jesseparker/vysko/stl/vysko/bearing_pillow_top_x3.stl

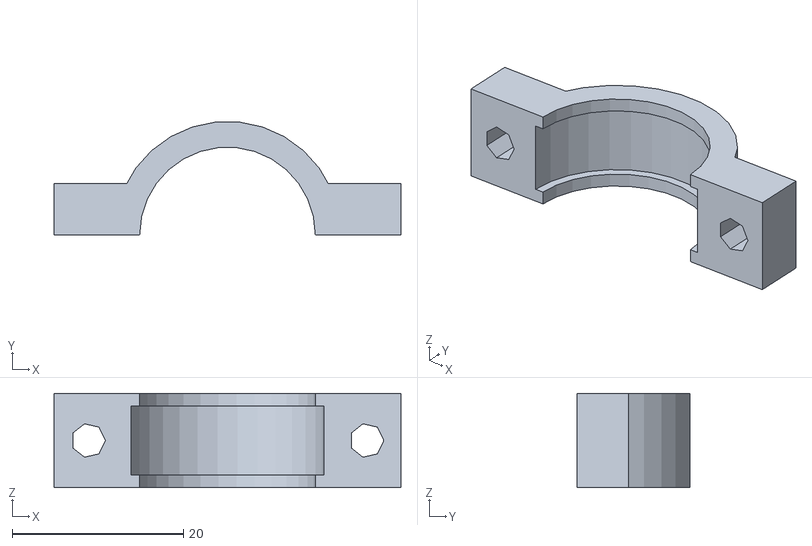
[picture p19: CAD file, 2020-10-01]
stl/vysko/bearing_pillow_top_x3.stl
40.5 x 13.2 x 11.0
