jesseparker/vysko/stl/vysko/funnel.stl

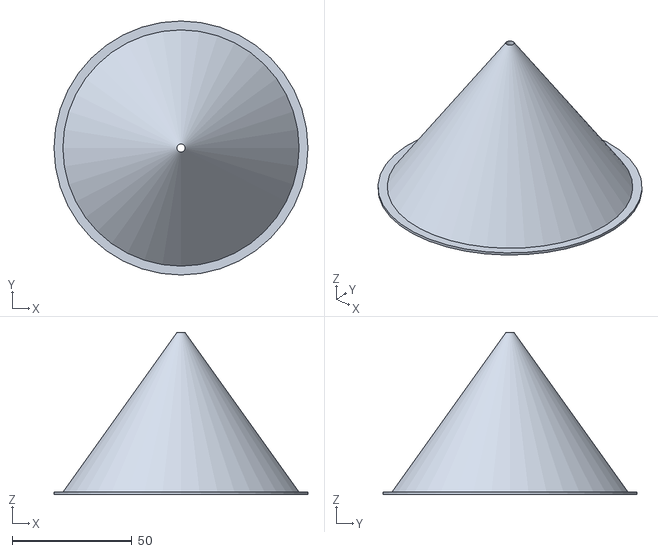
[picture p20: CAD file, 2020-10-01]
stl/vysko/funnel.stl
106.0 x 106.0 x 67.6
