jesseparker/vysko/stl/vysko/spinning_plate_cw.stl

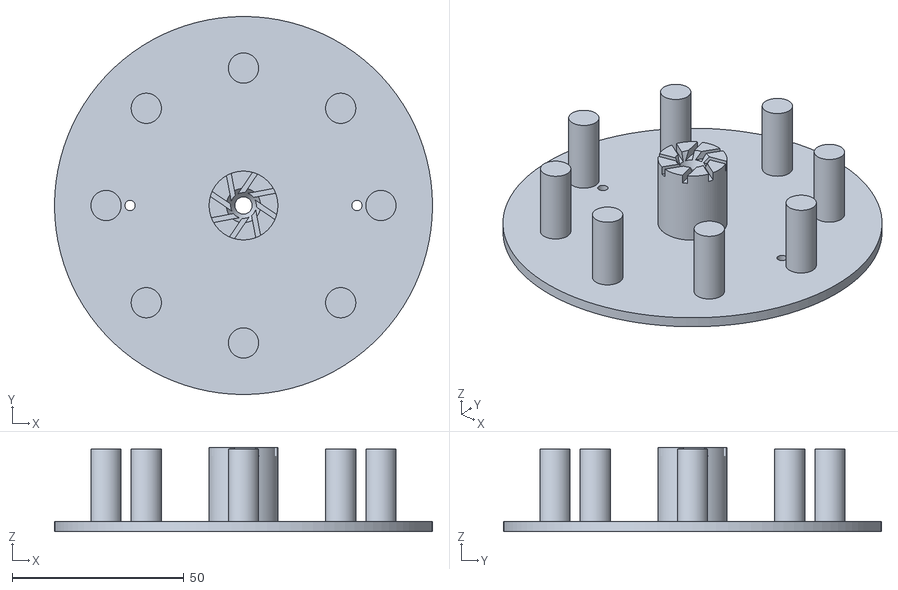
[picture p21: CAD file, 2020-10-01]
stl/vysko/spinning_plate_cw.stl
110.0 x 110.0 x 24.5
