jesseparker/vysko/stl/vysko/strut_drum.stl

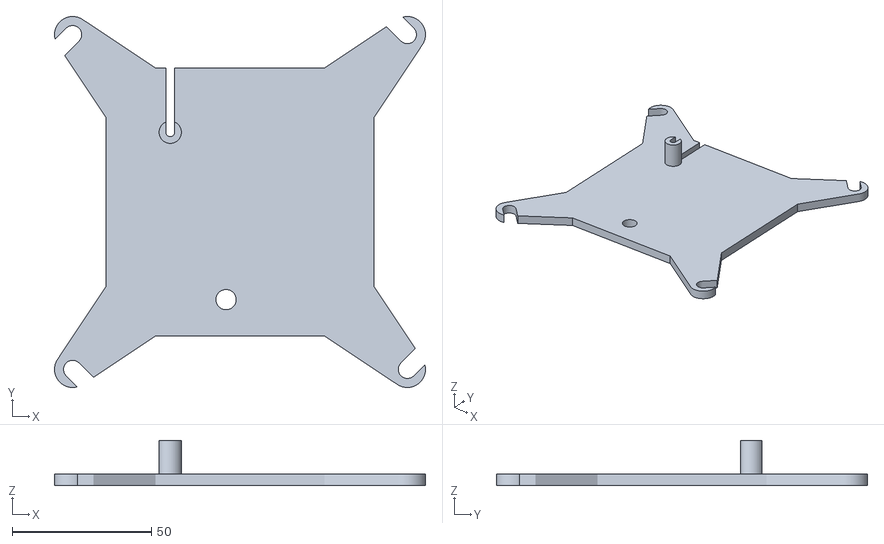
[picture p22: CAD file, 2020-10-01]
stl/vysko/strut_drum.stl
133.0 x 133.0 x 16.2
