jesseparker/vysko/stl/vysko/funnel_strut.stl

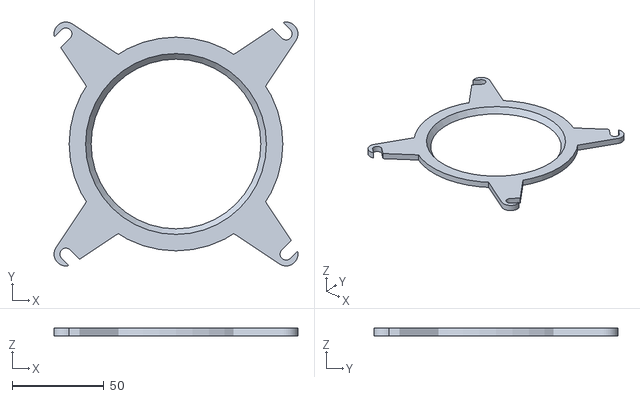
[picture p23: CAD file, 2020-10-01]
stl/vysko/funnel_strut.stl
133.0 x 133.0 x 4.25
