jesseparker/vysko/stl/vysko/strut_c.stl

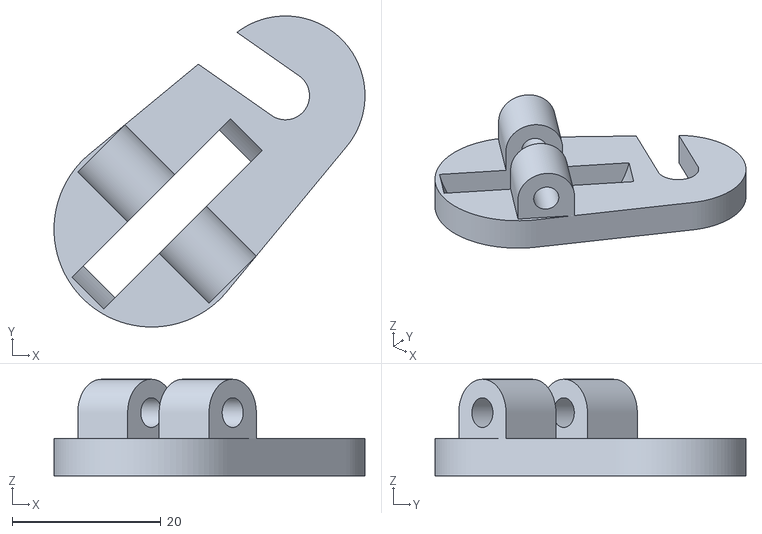
[picture p24: CAD file, 2020-10-01]
stl/vysko/strut_c.stl
41.9 x 41.9 x 13.0
