jesseparker/vysko/stl/vysko/spool_x19.stl

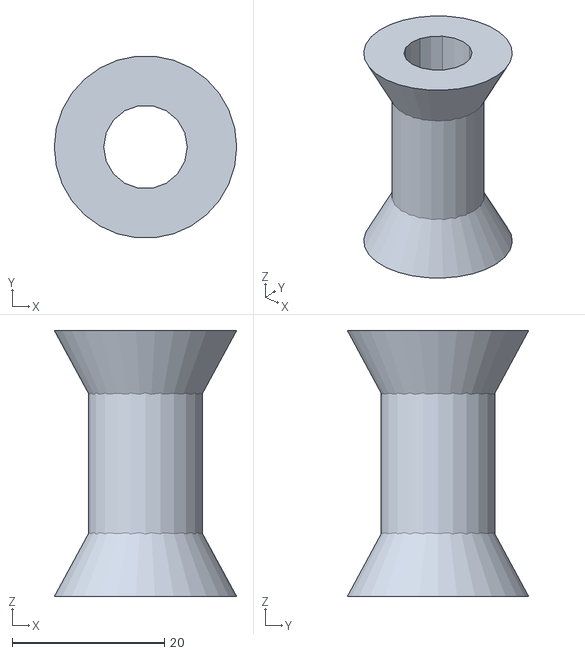
[picture p25: CAD file, 2020-10-01]
stl/vysko/spool_x19.stl
24.0 x 23.9 x 35.0
