jesseparker/vysko/stl/vysko/strut_r45_x3.stl

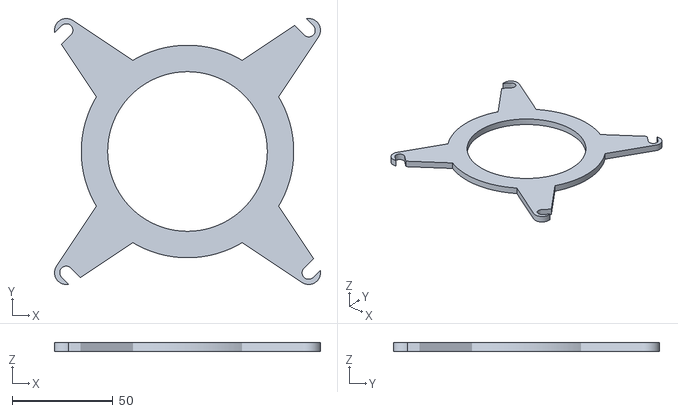
[picture p26: CAD file, 2020-10-01]
stl/vysko/strut_r45_x3.stl
131.7 x 131.7 x 4.25
