jesseparker/vysko/stl/vysko/driveshaft_pulley_20mm_x2.stl

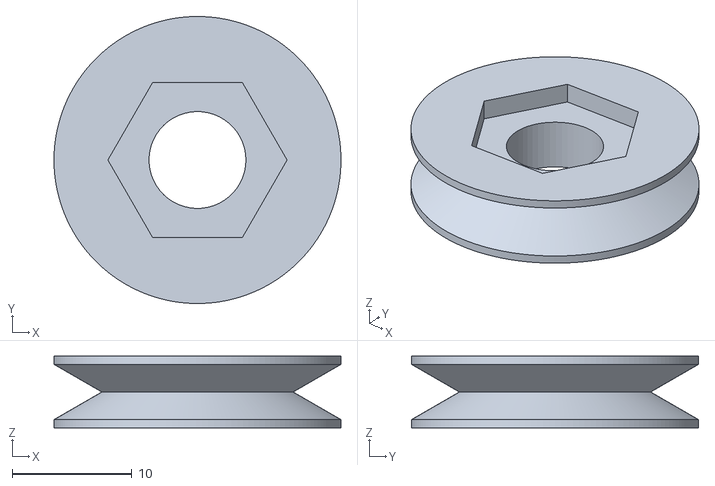
[picture p27: CAD file, 2020-10-01]
stl/vysko/driveshaft_pulley_20mm_x2.stl
24.0 x 24.0 x 6.00
