jesseparker/vysko/stl/vysko/reducer.stl

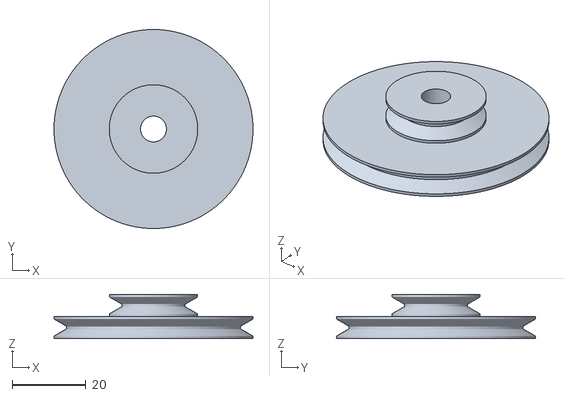
[picture p28: CAD file, 2020-10-01]
stl/vysko/reducer.stl
54.0 x 54.0 x 12.0
