jesseparker/vysko/stl/vysko/roller_x2.stl

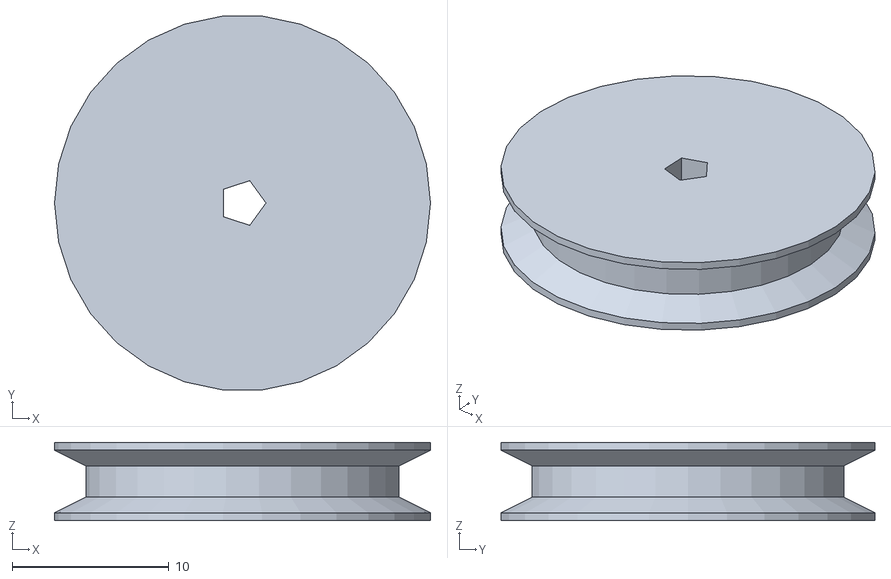
[picture p29: CAD file, 2020-10-01]
stl/vysko/roller_x2.stl
24.0 x 23.9 x 5.00
