jesseparker/vysko/stl/vysko/strut_side_x3.stl

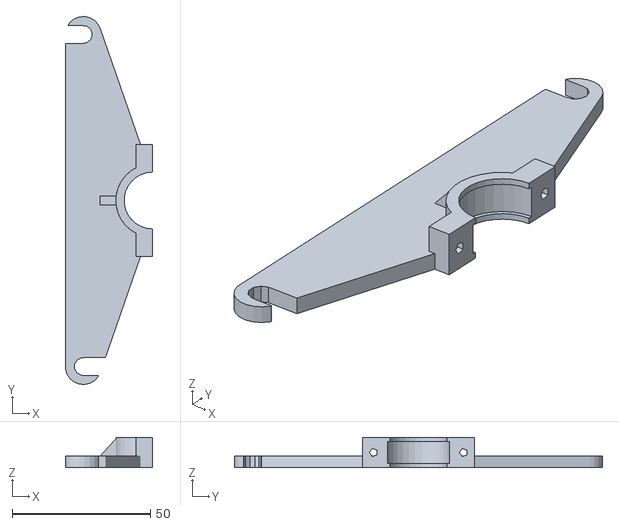
[picture p30: CAD file, 2020-10-01]
stl/vysko/strut_side_x3.stl
31.4 x 133.0 x 11.0
