jesseparker/vysko/sub_funnel.scad

use <sub_funnel.scad>       
use <funnel.scad>


module sub_funnel () {

funnel();

funnel_strut();

}

sub_funnel();
